EngVargas/FonteLinear/FonteLinear.Simula.LTSpice.asc

C1: cap; 4700µF
C2: cap; 4700µF
C3: cap; 1µF
C4: cap; 1µF
C5: cap; 1µF
C6: cap; 1µF
C7: cap; 1µF
D1: diode; DiodoSilicio
D2: diode; DiodoSilicio
D3: diode; DiodoSilicio
D4: diode; DiodoSilicio
L1: ind2; 100
L2: ind2; 1.395; Rser=0
L3: ind2; 1.395; Rser=0
R1: res; 15
R2: res; 15
R3: res; 100
R4: res; 100
R5: res; 240
R6: res; 1k
Rs: res; 0.1
U1: SpiceSymbol_Regulators
U2: SpiceSymbol_Regulators
U3: SpiceSymbol_Regulators
U4: SpiceSymbol_Regulators
V1: voltage; SINE(0 180 60)
Named nets: 0, VX, VY
.tran 0 167m 100m 0.0160m
.model DiodoIdeal D(Ron=0 Roff=1e16 Vfwd=0.0)
.model DiodoSilicio D(Ron=0 Roff=1e16 Vfwd=0.7)
K1 L1 L2 L3 0.99999
.lib SpiceModel_Regulators.mod
+
+
Obs.: R6 é um potenciômetro para ajustar o valor da tensão de saída
.MODEL Diodo1N4007 D( IS=76.9p RS=42.0m BV=1.00k IBV=5.00u
+ CJO=26.5p  M=0.333 N=1.45 TT=4.32u )
